KOEGlike/hackxpansion/blender/images/SideView.webp

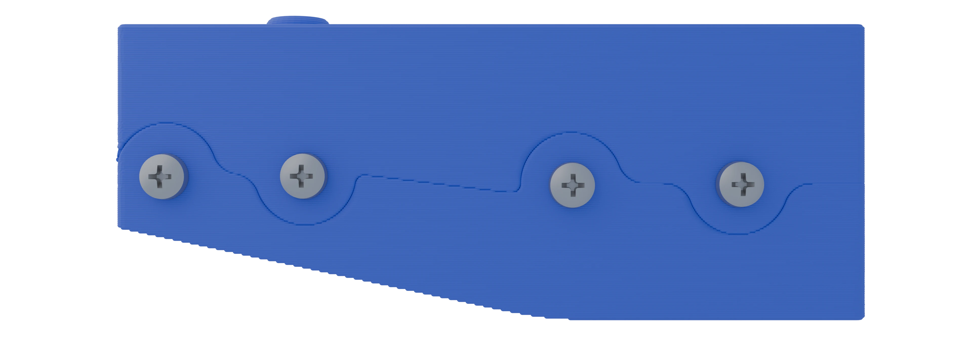
blender/images/SideView.webp
