KOEGlike/hackxpansion/firmware/xpanse/build.rs

//! This build script copies the `memory.x` file from the crate root into
//! a directory where the linker can always find it at build time.
//! For many projects this is optional, as the linker always searches the
//! project root directory -- wherever `Cargo.toml` is. However, if you
//! are using a workspace or have a more complicated build setup, this
//! build script becomes required. Additionally, by requesting that
//! Cargo re-run the build script whenever `memory.x` is changed,
//! updating `memory.x` ensures a rebuild of the application with the
//! new memory settings.

use std::env;
use std::fs::File;
use std::io::Write;
use std::path::PathBuf;

fn main() {
    let slint_config = slint_build::CompilerConfiguration::new()
        .embed_resources(slint_build::EmbedResourcesKind::EmbedForSoftwareRenderer);
    slint_build::compile_with_config("ui/app_picker.slint", slint_config)
        .expect("failed to compile app picker UI");
    // Put `memory.x` in our output directory and ensure it's
    // on the linker search path.
    let out = &PathBuf::from(env::var_os("OUT_DIR").unwrap());
    File::create(out.join("memory.x"))
        .unwrap()
        .write_all(include_bytes!("memory.x"))
        .unwrap();
    println!("cargo:rustc-link-search={}", out.display());

    // By default, Cargo will re-run a build script whenever any file in the
    // project changes. Keep the rebuild triggers focused on files this script
    // consumes.
    println!("cargo:rerun-if-changed=memory.x");
    println!("cargo:rerun-if-changed=ui/app_picker.slint");
    println!("cargo:rerun-if-changed=ui/fonts/ShareTechMono-Regular.ttf");

    println!("cargo:rustc-link-arg-bins=--nmagic");
    println!("cargo:rustc-link-arg-bins=-Tlink.x");
    println!("cargo:rustc-link-arg-bins=-Tdefmt.x");
}
