KOEGlike/hackxpansion/firmware/xpanse/src/lib.rs

#![no_std]
extern crate alloc;

pub mod adc;
pub mod adc_mapping;
mod app_loader;
mod app_picker;
pub mod bus;
pub mod core_app;
pub mod core_driver;
pub mod display;
pub mod load_driver;
pub mod resource_split;
